cervidwithmoped/carrot-fan/Carrot Proto 2.stl

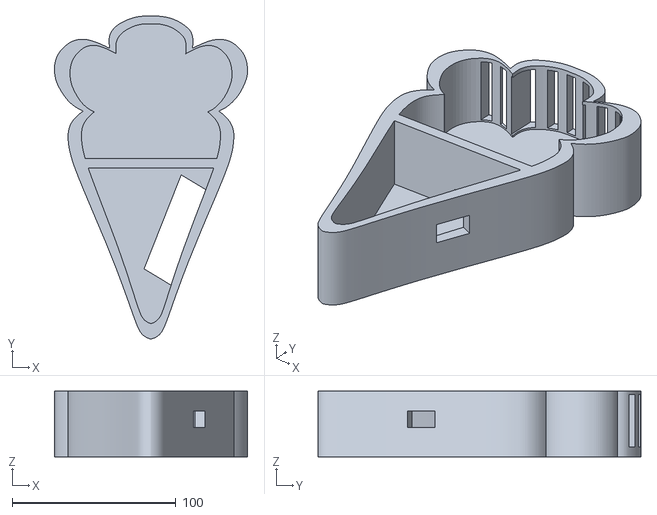
[picture p12: CAD file, 2024-02-20, last stored version]
Carrot Proto 2.stl
117.9 x 197.2 x 40.0
