cervidwithmoped/carrot-fan/Carrot.stl

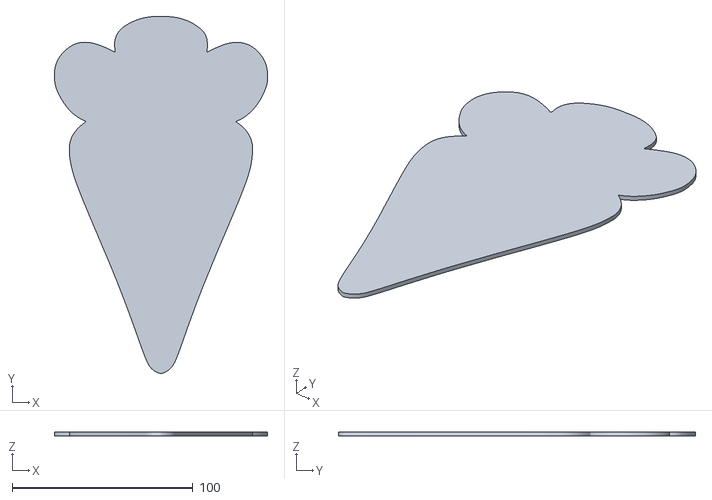
[picture p13: CAD file, 2024-02-20, last stored version]
Carrot.stl
117.9 x 197.2 x 2.00
